Shadow220108/Hermes/PCB/Hermes.kicad_sch

## KiCad design PCB/Hermes.kicad_sch (2026-04-17)

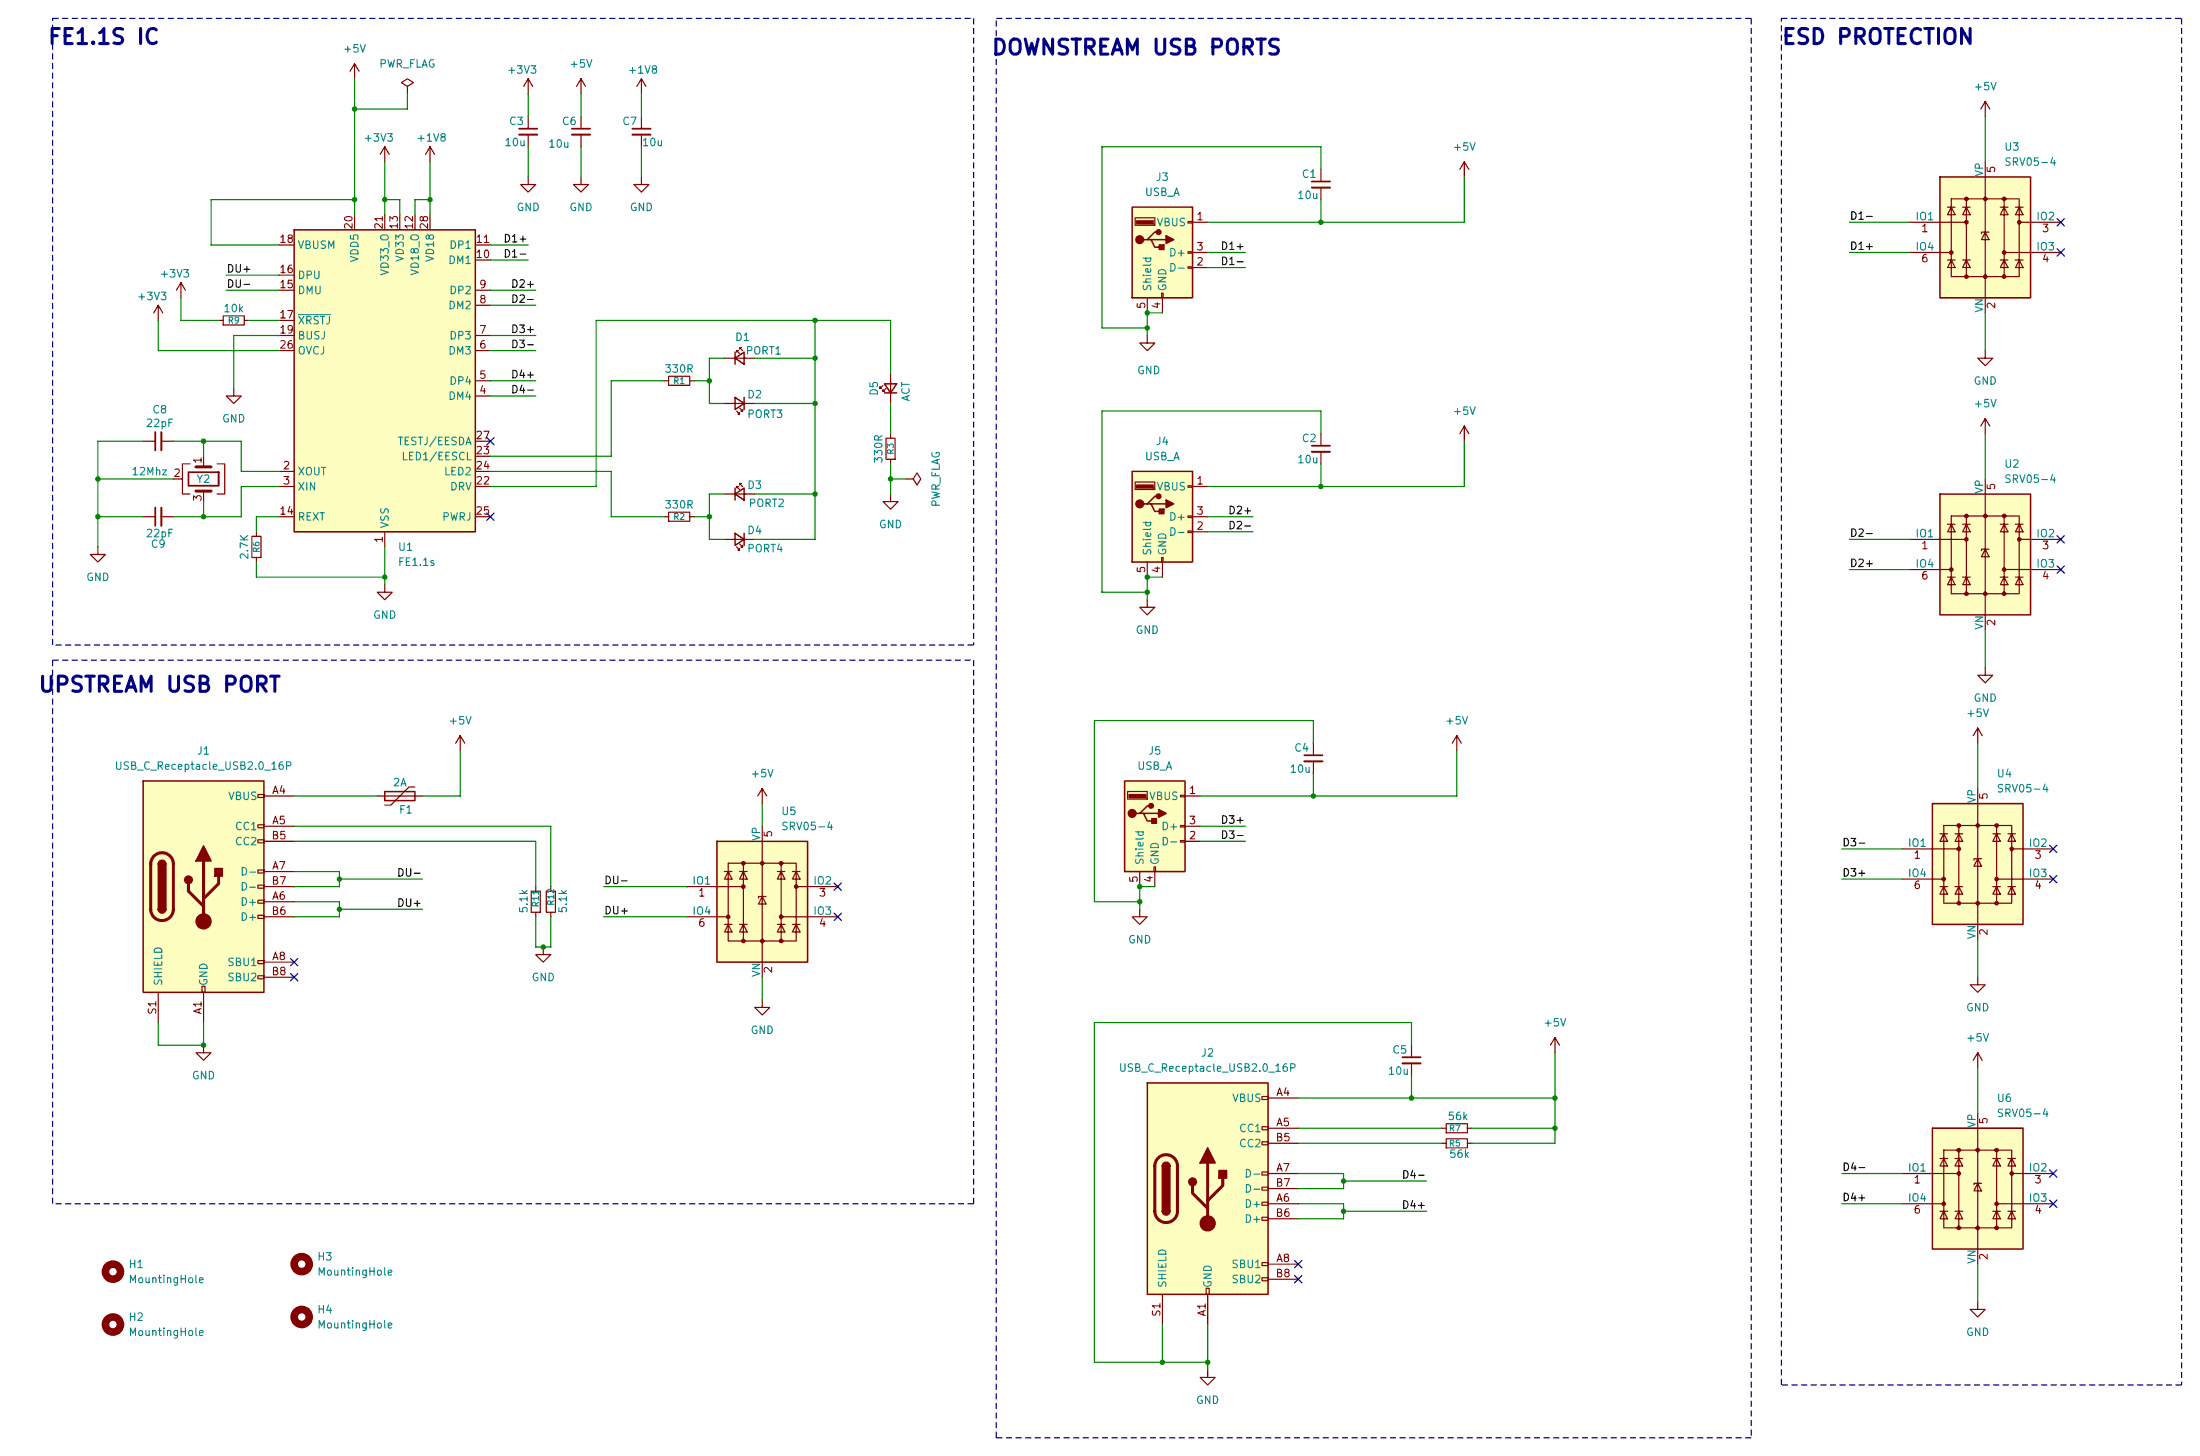
[picture p17: schematic Hermes.kicad_sch]

Parts:
C1, C2, C3, C4, C5, C6, C7: 10u; C_0603_1608Metric
C8, C9: 22pF; C_0805_2012Metric
D1: PORT1; LED_D3.0mm
D2: PORT3; LED_D3.0mm
D3: PORT2; LED_D3.0mm
D4: PORT4; LED_D3.0mm
D5: ACT; LED_D3.0mm
F1: 2A; Fuse_1206_3216Metric
H1, H2, H3, H4: MountingHole; MountingHole_2.5mm
J1, J2: USB_C_Receptacle_USB2.0_16P; USB_C_Receptacle_GCT_USB4105-xx-A_16P_TopMnt_Horizontal
J3, J4, J5: USB_A; USB_A_Molex_67643_Horizontal
R1, R2, R3: 330R; R_0805_2012Metric
R5, R7: 56k; R_0805_2012Metric
R6: 2.7K; R_0603_1608Metric
R9: 10k; R_0805_2012Metric
R11, R12: 5.1k; R_0805_2012Metric
U1: FE1.1s; SSOP-28_3.9x9.9mm_P0.635mm
U2, U3, U4, U5, U6: SRV05-4; SOT-23-6-routable
Y2: 12Mhz; Crystal_SMD_5032-4Pin_5.0x3.2mm

Connections:
+1V8: C7.1, U1.12 (VD18_O), U1.28 (VD18)
+3V3: C3.1, R9.1, U1.13 (VD33), U1.21 (VD33_O), U1.26 (OVCJ)
+5V: C1.2, C2.2, C4.2, C5.2, C6.1, F1.2, J2.A4 (VBUS), J2.A9 (VBUS), J2.B4 (VBUS), J2.B9 (VBUS), J3.1 (VBUS), J4.1 (VBUS), J5.1 (VBUS), R5.2, R7.2, U1.18 (VBUSM), U1.20 (VDD5), U2.5 (VP), U3.5 (VP), U4.5 (VP), U5.5 (VP), U6.5 (VP)
D1+: J3.3 (D+), U1.11 (DP1), U3.6 (IO4)
D1-: J3.2 (D-), U1.10 (DM1), U3.1 (IO1)
D2+: J4.3 (D+), U1.9 (DP2), U2.6 (IO4)
D2-: J4.2 (D-), U1.8 (DM2), U2.1 (IO1)
D3+: J5.3 (D+), U1.7 (DP3), U4.6 (IO4)
D3-: J5.2 (D-), U1.6 (DM3), U4.1 (IO1)
D4+: J2.A6 (D+), J2.B6 (D+), U1.5 (DP4), U6.6 (IO4)
D4-: J2.A7 (D-), J2.B7 (D-), U1.4 (DM4), U6.1 (IO1)
DU+: J1.A6 (D+), J1.B6 (D+), U1.16 (DPU), U5.6 (IO4)
DU-: J1.A7 (D-), J1.B7 (D-), U1.15 (DMU), U5.1 (IO1)
GND: C1.1, C2.1, C3.2, C4.1, C5.1, C6.2, C7.2, C8.1, C9.1, J1.A1 (GND), J1.A12 (GND), J1.B1 (GND), J1.B12 (GND), J1.S1 (SHIELD), J2.A1 (GND), J2.A12 (GND), J2.B1 (GND), J2.B12 (GND), J2.S1 (SHIELD), J3.4 (GND), J3.5 (Shield), J4.4 (GND), J4.5 (Shield), J5.4 (GND), J5.5 (Shield), R3.1, R6.1, R11.1, R12.2, U1.1 (VSS), U1.19 (BUSJ), U2.2 (VN), U3.2 (VN), U4.2 (VN), U5.2 (VN), U6.2 (VN), Y2.2 (G), Y2.4 (G)
unnamed: C8.2, U1.2 (XOUT), Y2.1
unnamed: C9.2, U1.3 (XIN), Y2.3
unnamed: D1.1 (K), D2.2 (A), R1.2
unnamed: D1.2 (A), D2.1 (K), D3.2 (A), D4.1 (K), D5.2 (A), U1.22 (DRV)
unnamed: D3.1 (K), D4.2 (A), R2.2
unnamed: D5.1 (K), R3.2
unnamed: F1.1, J1.A4 (VBUS), J1.A9 (VBUS), J1.B4 (VBUS), J1.B9 (VBUS)
unnamed: J1.A5 (CC1), R12.1
unnamed: J1.B5 (CC2), R11.2
unnamed: J2.A5 (CC1), R7.1
unnamed: J2.B5 (CC2), R5.1
unnamed: R1.1, U1.23 (LED1/EESCL)
unnamed: R2.1, U1.24 (LED2)
unnamed: R6.2, U1.14 (REXT)
unnamed: R9.2, U1.17 (~XRSTJ)

Notes on the sheet:
ESD PROTECTION
FE1.1S IC
UPSTREAM USB PORT
DOWNSTREAM USB PORTS
